dakk/gemma-grezza/uncut-gem/sweep_array.h

// NEW MASTER LOOP

// 2854MHz start, 0.25MHz steps,
// byte sweepArr0_25[128][6][5] = {
byte sweepArr[128][6][5] = {
{{5, 0x00, 0x58, 0x00, 0x05}, {4, 0x00, 0x86, 0x43, 0x24}, {3, 0x00, 0x04, 0x00, 0x03}, {2, 0x38, 0x00, 0xBE, 0x42}, {1, 0x00, 0x00, 0x80, 0xC9}, {0, 0x00, 0x72, 0x00, 0x40}},
{{5, 0x00, 0x58, 0x00, 0x05}, {4, 0x00, 0x86, 0x43, 0x24}, {3, 0x00, 0x04, 0x00, 0x03}, {2, 0x38, 0x00, 0xBE, 0x42}, {1, 0x00, 0x00, 0x81, 0x91}, {0, 0x00, 0x72, 0x00, 0x88}},
{{5, 0x00, 0x58, 0x00, 0x05}, {4, 0x00, 0x86, 0x43, 0x24}, {3, 0x00, 0x04, 0x00, 0x03}, {2, 0x38, 0x00, 0xBE, 0x42}, {1, 0x00, 0x00, 0x80, 0xC9}, {0, 0x00, 0x72, 0x00, 0x48}},
{{5, 0x00, 0x58, 0x00, 0x05}, {4, 0x00, 0x86, 0x43, 0x24}, {3, 0x00, 0x04, 0x00, 0x03}, {2, 0x38, 0x00, 0xBE, 0x42}, {1, 0x00, 0x00, 0x81, 0x91}, {0, 0x00, 0x72, 0x00, 0x98}},
{{5, 0x00, 0x58, 0x00, 0x05}, {4, 0x00, 0x86, 0x43, 0x24}, {3, 0x00, 0x04, 0x00, 0x03}, {2, 0x38, 0x00, 0xBE, 0x42}, {1, 0x00, 0x00, 0x80, 0x29}, {0, 0x00, 0x72, 0x00, 0x10}},
{{5, 0x00, 0x58, 0x00, 0x05}, {4, 0x00, 0x86, 0x43, 0x24}, {3, 0x00, 0x04, 0x00, 0x03}, {2, 0x38, 0x00, 0xBE, 0x42}, {1, 0x00, 0x00, 0x81, 0x91}, {0, 0x00, 0x72, 0x00, 0xA8}},
{{5, 0x00, 0x58, 0x00, 0x05}, {4, 0x00, 0x86, 0x43, 0x24}, {3, 0x00, 0x04, 0x00, 0x03}, {2, 0x38, 0x00, 0xBE, 0x42}, {1, 0x00, 0x00, 0x80, 0xC9}, {0, 0x00, 0x72, 0x00, 0x58}},
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
{{6, 0x00, 0x00, 0x00, 0x00}, {6, 0x00, 0x00, 0x00, 0x00}, {6, 0x00, 0x00, 0x00, 0x00}, {6, 0x00, 0x00, 0x00, 0x00}, {6, 0x00, 0x00, 0x00, 0x00}, {0, 0x00, 0x8E, 0x91, 0xB8}},
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
